scimusmn/tsck-dna-puzzle/arduino/controller/SerialController.h

#pragma once

#ifdef UNIT_TEST
#include "tests/FakeSerial.h"
#else
#include <Arduino.h>
#endif

#include "FixedSizeString.h"
#include "LookupTable.h"

namespace smm {

    typedef void (*voidCallback)();
    typedef void (*stringCallback)(const char*);
    typedef void (*intCallback)(int);
    typedef void (*floatCallback)(float);


    /* ~~~~~~~~~~~~~~~~~~~~~~~~~~~~~~~~~~~~~~~~~~~~~~~~~~~~~~~~~~~~~~~~
     *
     * SerialCallback
     *
     * ~~~~~~~~~~~~~~~~~~~~~~~~~~~~~~~~~~~~~~~~~~~~~~~~~~~~~~~~~~~~~~~~
     */

    struct SerialCallback {
	SerialCallback() { valueType = NONE; }
	SerialCallback(voidCallback cb)   { valueType = VOID;   callback.v = cb; }
	SerialCallback(stringCallback cb) { valueType = STRING; callback.s = cb; }
	SerialCallback(intCallback cb)    { valueType = INT;    callback.i = cb; }
	SerialCallback(floatCallback cb)  { valueType = FLOAT;  callback.f = cb; }

	typedef enum {
	    NONE,
	    VOID,
	    STRING,
	    INT,
	    FLOAT
	} ValueType;

	ValueType valueType;

	union {
	    voidCallback v;
	    stringCallback s;
	    intCallback i;
	    floatCallback f;
	} callback;

	void operator()(const char *value) {
	    switch (valueType) {
	    case NONE:
		break;
		
	    case VOID:
		callback.v();
		break;
      
	    case STRING:
		callback.s(value);
		break;

	    case INT:
		callback.i(atoi(value));
		break;

	    case FLOAT:
		callback.f(atof(value));
		break;

	    default:
		// bad valueType, do nothing
		break;
	    }
	}
    };


    /* ~~~~~~~~~~~~~~~~~~~~~~~~~~~~~~~~~~~~~~~~~~~~~~~~~~~~~~~~~~~~~~~~
     *
     * SerialController
     *
     * ~~~~~~~~~~~~~~~~~~~~~~~~~~~~~~~~~~~~~~~~~~~~~~~~~~~~~~~~~~~~~~~~
     */

    template<unsigned int MAX_CALLBACKS=16,
	     size_t MAX_KEY_LEN=32, size_t MAX_VAL_LEN=MAX_KEY_LEN>
    class SerialController {
    public:
	void setup(long baudrate=115200) {
	    Serial.begin(baudrate);
	    reset();
	}
  
	// overloaded callback-adding functions
	void addCallback(const char *key, voidCallback cb) {
	    m_callbacks.add(key, SerialCallback(cb));
	}
	void addCallback(const char *key, stringCallback cb) {
	    m_callbacks.add(key, SerialCallback(cb));
	}
	void addCallback(const char *key, intCallback cb) {
	    m_callbacks.add(key, SerialCallback(cb));
	}
	void addCallback(const char *key, floatCallback cb) {
	    m_callbacks.add(key, SerialCallback(cb));
	}
  
	// message sending
	void send(const char *messageKey, const char *messageValue, bool cleanValue=true) {
	    smm::FixedSizeString<MAX_KEY_LEN> key;
	    smm::FixedSizeString<MAX_VAL_LEN> value;
	    
	    cleanString(key, messageKey);
	    if (cleanValue)
		cleanString(value, messageValue);
	    else
		value = messageValue;

	    Serial.print("{");
	    Serial.print(key.c_str());
	    Serial.print(":");
	    Serial.print(value.c_str());
	    Serial.println("}");
	}
	void send(const char *messageKey) { send(messageKey, "1"); }
	void send(const char *messageKey, int messageValue) {
	    smm::FixedSizeString<MAX_VAL_LEN> value;
	    value = messageValue;
	    send(messageKey, value.c_str());
	}
	void send(const char *messageKey, float messageValue) {
	    smm::FixedSizeString<MAX_VAL_LEN> value;
	    value = messageValue;
	    send(messageKey, value.c_str());
	}
	

	// updating
	void update() {
	    while(Serial.available())
		eatCharacter(Serial.read());
	}


	// size info
	size_t maxKeyLength() { return MAX_KEY_LEN; }
	size_t maxValueLength() { return MAX_VAL_LEN; }
	unsigned int maxNumCallbacks() { return MAX_CALLBACKS; }

	unsigned int numCallbacks() { return m_callbacks.size(); }

    private:
	smm::LookupTable<smm::FixedSizeString<MAX_KEY_LEN>, SerialCallback, MAX_CALLBACKS> m_callbacks;
	smm::FixedSizeString<MAX_KEY_LEN> m_key;
	smm::FixedSizeString<MAX_VAL_LEN> m_value;
	bool m_keyOverflowed;

	enum {
	    WAIT_FOR_START,
	    PARSE_KEY,
	    PARSE_VALUE,
	} m_state;

	
	void eatCharacter(char c) {
	    switch (m_state) {
	    case WAIT_FOR_START:
		if (c == '{')
		    m_state = PARSE_KEY;
		break;

	    case PARSE_KEY:
		if (c == '{') {
		    // malformed input, new message starting
		    reset();
		    m_state = PARSE_KEY;
		}
		else if (c == '}')
		    // malformed input, ignore
		    reset();
		else if (c == ':')
		    m_state = PARSE_VALUE;
		else {
		    if (m_key.length() == m_key.maxLength())
			m_keyOverflowed = true;
		    m_key.append(c);
		}
		break;

	    case PARSE_VALUE:
		if (c == '{') {
		    // malformed input, new message starting
		    reset();
		    m_state = PARSE_KEY;
		}
		else if (c == ':')
		    // malformed input, ignore
		    reset();
		else if (c == '}')
		    handleMessage();
		else
		    m_value.append(c);
		break;

	    default:
		// something's gone wrong, reset
		reset();
		break;
	    }
	}

	
	void handleMessage() {
	    SerialCallback* cb = m_callbacks[m_key.c_str()];
	    if (m_keyOverflowed)
		send("warning", "Key overflow!");
	    else if (cb == nullptr)
		unknownMessage();
	    else
		(*cb)(m_value.c_str());
	    reset();
	}


	void unknownMessage() {
	    Serial.print("{unknown-message:");
	    Serial.print(m_key.c_str());
	    Serial.println("}");
	}
	

	void reset() {
	    m_state = WAIT_FOR_START;
	    m_key.clear();
	    m_value.clear();
	    m_keyOverflowed = false;
	}

	template<size_t size>
	void cleanString(smm::FixedSizeString<size>& dest, const char *source) {
	    size_t length = strlen(source);
	    for (int i=0; i<length; i++) {
		char c = source[i];
		if (c == '{' || c == ':' || c == '}')
		    continue;
		dest.append(c);
	    }
	}
    };


    template<unsigned int MAX_CALLBACKS=16,
	     size_t MAX_KEY_LEN=32, size_t MAX_VAL_LEN=MAX_KEY_LEN>
    class SteleSerialController : public SerialController<MAX_CALLBACKS, MAX_KEY_LEN, MAX_VAL_LEN> {
    public:
	void setup(long baudrate=115200) {
	    Serial.begin(baudrate);
	    while (!Serial);
	    bool handshake = false;
	    while (!handshake) {
		if (Serial.available())
		    handshake = Serial.read() == '{';
	    }
	    this->send("arduino-ready");
	}
    };
}
